dunkelstern/LittleSpeaker/docs/electronics/firebeetle.png

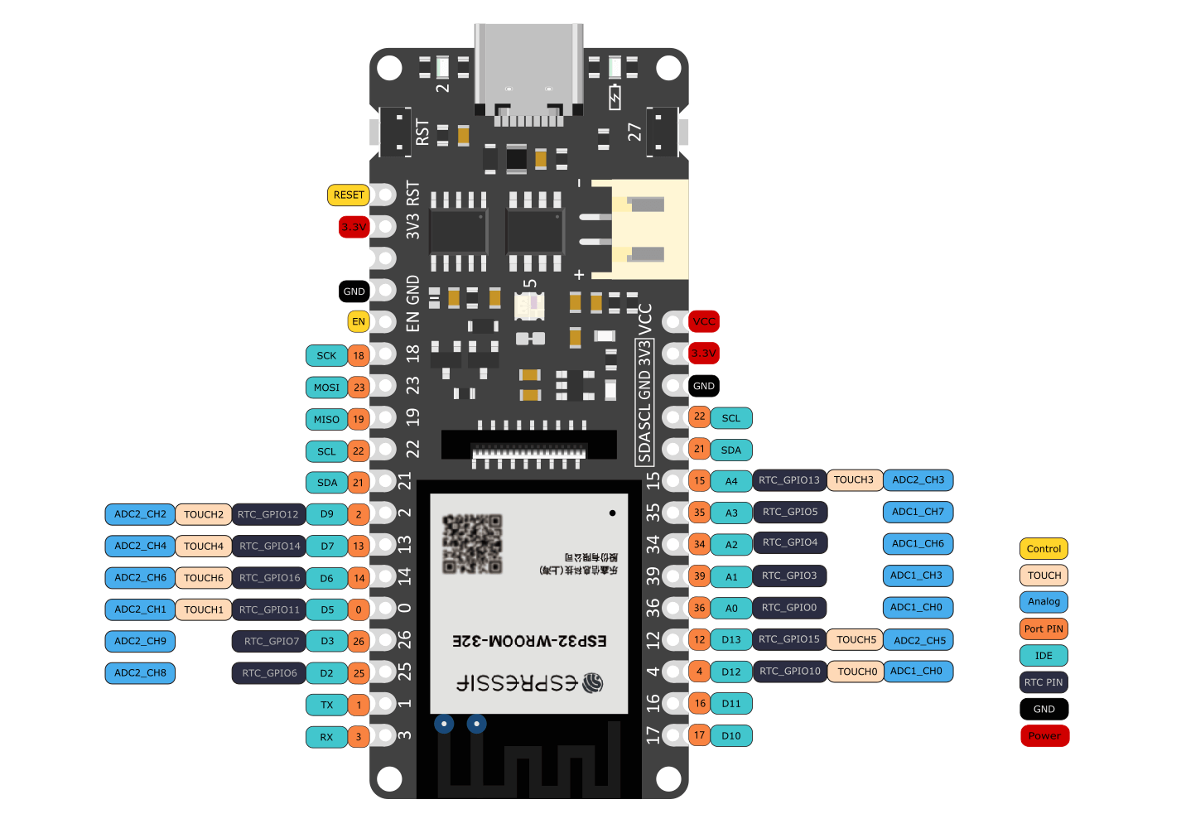
docs/electronics/firebeetle.png
