dunkelstern/LittleSpeaker/docs/electronics/stuffing.jpg

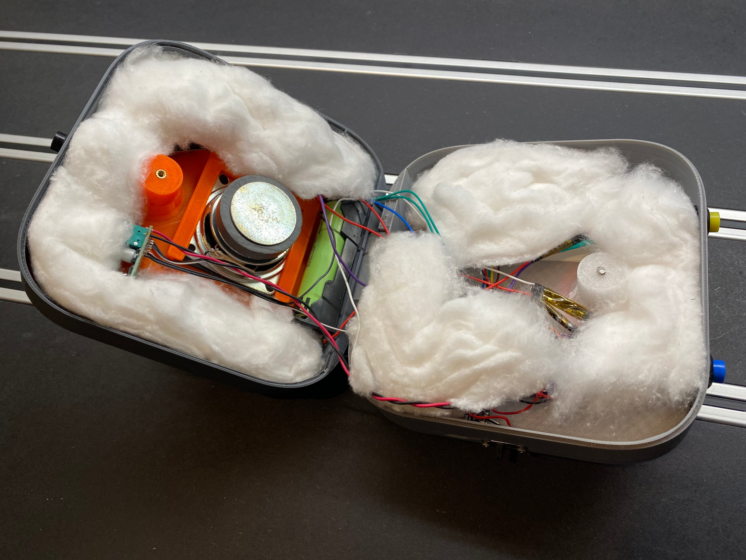
docs/electronics/stuffing.jpg
