dunkelstern/LittleSpeaker/src/AudioOutputFIlter3BandEQ.cpp

#include <Arduino.h>
#include "AudioOutputFilter3BandEQ.h"

static const PRECISION vsa = PRECISION(1.0 / 536870911.0);   // Very small amount (Denormal Fix)

AudioOutputFilter3BandEQ::AudioOutputFilter3BandEQ(AudioOutput *sink, int lowFreq, int highFreq) {
    this->sink = sink;
    this->lowFreq = lowFreq;
    this->highFreq = highFreq;

    Serial.printf("EQ initialized with low = %d, high = %d\n", lowFreq, highFreq);

    for (int i = 0; i < 2; i++) {
        EQState *state = this->state + i;

        state->lf = PRECISION(0);
        state->f1p0 = PRECISION(0);

        state->hf = PRECISION(0);
        state->f2p0 = PRECISION(0);

        // Set Low/Mid/High gains to unity
        state->lg = PRECISION(1.0);
        state->mg = PRECISION(1.0);
        state->hg = PRECISION(1.0);
    }

    Serial.printf("Value test: vsa = %d.%d (%f)\n", vsa.getInteger(), vsa.getFraction(), (float)vsa);
}


AudioOutputFilter3BandEQ::~AudioOutputFilter3BandEQ() {
}

bool AudioOutputFilter3BandEQ::SetRate(int hz) {
    for (int i = 0; i < 2; i++) {
        // Calculate filter cutoff frequencies
        this->state[i].lf = PRECISION(2.0f * sin(M_PI * ((double)lowFreq / (double)hz)));
        this->state[i].hf = PRECISION(2.0f * sin(M_PI * ((double)highFreq / (double)hz)));
    }

    Serial.printf("Low freq %0.2f (%d.%d), high freq %0.2f (%d.%d)\n",
        (float)this->state[0].lf, this->state[0].lf.getInteger(), this->state[0].lf.getFraction(),
        (float)this->state[0].hf, this->state[0].hf.getInteger(), this->state[0].hf.getFraction()
    );

    this->sample_rate = hz;
    return sink->SetRate(hz);
}

void AudioOutputFilter3BandEQ::setBandGains(float low, float mid, float high) {
    for(int i = 0; i < 2; i++) {
        this->state[i].lg = PRECISION((float)low);
        this->state[i].mg = PRECISION((float)mid);
        this->state[i].hg = PRECISION((float)high);
    }
    Serial.printf("EQ gains set to %0.2f (%d.%d), %0.2f (%d.%d), %0.2f (%d.%d)\n",
        (float)this->state[0].lg, this->state[0].lg.getInteger(), this->state[0].lg.getFraction(),
        (float)this->state[0].mg, this->state[0].mg.getInteger(), this->state[0].mg.getFraction(),
        (float)this->state[0].hg, this->state[0].hg.getInteger(), this->state[0].hg.getFraction()
    );
}

bool AudioOutputFilter3BandEQ::SetBitsPerSample(int bits) {
    return sink->SetBitsPerSample(bits);
}

bool AudioOutputFilter3BandEQ::SetChannels(int channels) {
    this->channels = channels;
    return sink->SetChannels(channels);
}

bool AudioOutputFilter3BandEQ::SetGain(float gain) {
    return sink->SetGain(gain);
}

bool AudioOutputFilter3BandEQ::begin() {
    return sink->begin();
}

bool AudioOutputFilter3BandEQ::ConsumeSample(int16_t sample[2]) {
    PRECISION l(0), m(0), h(0);      // Low / Mid / High - Sample Values
    int32_t result;

    for(int i = 0; i < this->channels; i++) {
        EQState *es = this->state + i;
        PRECISION s = PRECISION((double)sample[i] / (double)(INT16_MAX + 1) / 2.0);
 
        // Filter #1 (lowpass)
        es->f1p0  += (es->lf * (s        - es->f1p0)) + vsa;
        l = es->f1p0;

        // Filter #2 (highpass)
        es->f2p0  += (es->hf * (s        - es->f2p0)) + vsa;
        h = s - es->f2p0;

        // Calculate midrange (signal - (low + high))
        m = s - (h + l);

        // Scale, Combine and store

        l         *= es->lg;
        m         *= es->mg;
        h         *= es->hg;

        result = round((double)(l + m + h) * (double)INT16_MAX);

        // clip
        if (result < INT16_MIN) {
            result = INT16_MIN;
        } else if (result > INT16_MAX) {
            result = INT16_MAX;
        }

        // save
        sample[i] = (int16_t)result;
   }

    if (this->channels == 1) {
        sample[1] = sample[0];
    }
    return sink->ConsumeSample(sample);
}

bool AudioOutputFilter3BandEQ::stop() {
    for (int i = 0; i < 2; i++) {
        EQState *state = this->state + i;

        state->lf = PRECISION(0);
        state->f1p0 = PRECISION(0);

        state->hf = PRECISION(0);
        state->f2p0 = PRECISION(0);

        // Set Low/Mid/High gains to unity
        state->lg = PRECISION(1.0);
        state->mg = PRECISION(1.0);
        state->hg = PRECISION(1.0);
    }

    return sink->stop();
}


void AudioOutputFilter3BandEQ::processBuffer(int16_t *samples, int len, int stride, int channels) {
    PRECISION l(0), m(0), h(0);      // Low / Mid / High - Sample Values
    int32_t result;

    for(int j = 0; j < len; j+=stride) {
        int16_t *sample = samples + j;

        for(int i = 0; i < channels; i++) {
            EQState *es = this->state + i;
            PRECISION s = PRECISION((double)sample[i] / (double)(INT16_MAX + 1) / 2.0);
    
            // Filter #1 (lowpass)
            es->f1p0  += (es->lf * (s        - es->f1p0)) + vsa;
            l = es->f1p0;

            // Filter #2 (highpass)
            es->f2p0  += (es->hf * (s        - es->f2p0)) + vsa;
            h = s - es->f2p0;

            // Calculate midrange (signal - (low + high))
            m = s - (h + l);

            // Scale, Combine and store

            l         *= es->lg;
            m         *= es->mg;
            h         *= es->hg;

            result = round((double)(l + m + h) * (double)INT16_MAX);

            // clip
            if (result < INT16_MIN) {
                result = INT16_MIN;
            } else if (result > INT16_MAX) {
                result = INT16_MAX;
            }

            // save
            sample[i] = (int16_t)result;
        }

        if ((channels == 1) && (stride == 2)) {
            sample[1] = sample[0];
        }
    }
}
